juanma010901/Quadruped-Robot/Diseños/files/F_cover.stl

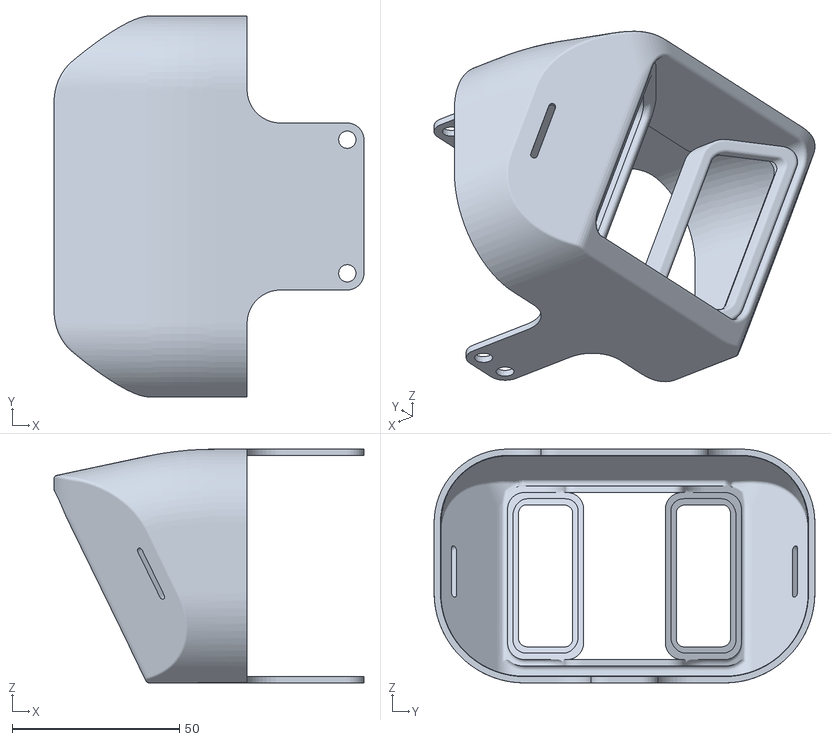
[picture p19: CAD file, 2023-06-25]
Diseños/files/F_cover.stl
92.8 x 114.0 x 70.0
