juanma010901/Quadruped-Robot/Diseños/files/V1.00_Nose.stl

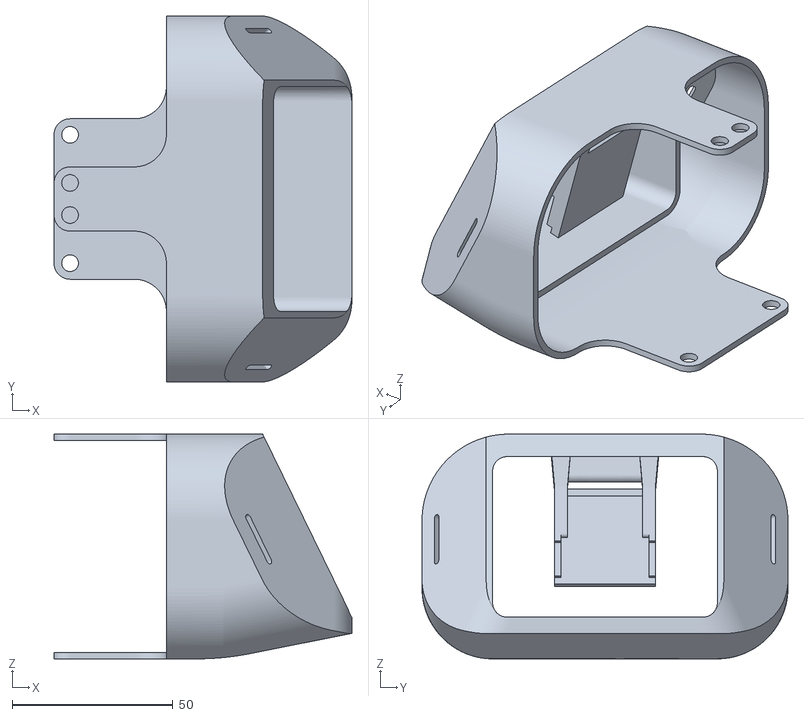
[picture p20: CAD file, 2023-06-25]
Diseños/files/V1.00_Nose.stl
92.8 x 114.0 x 70.0
