juanma010901/Quadruped-Robot/Diseños/files/Rear_Cover.stl

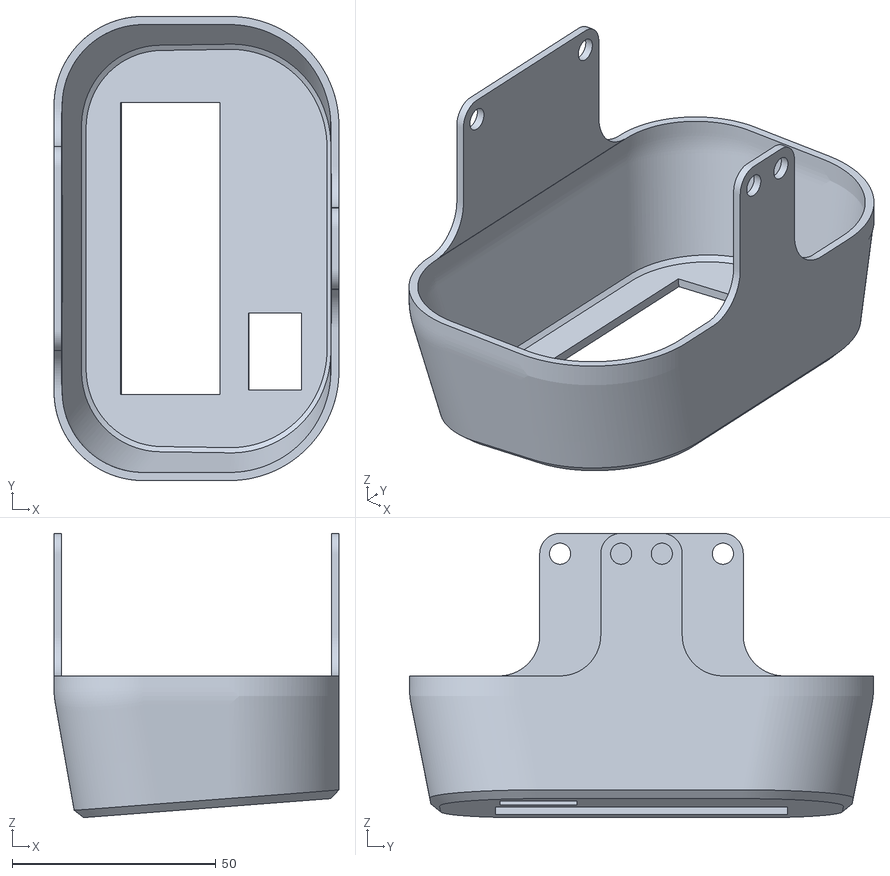
[picture p21: CAD file, 2023-06-25]
Diseños/files/Rear_Cover.stl
70.0 x 114.0 x 69.8
