juanma010901/Quadruped-Robot/Diseños/files/V1.01_Front_Shoulder_Inner.stl

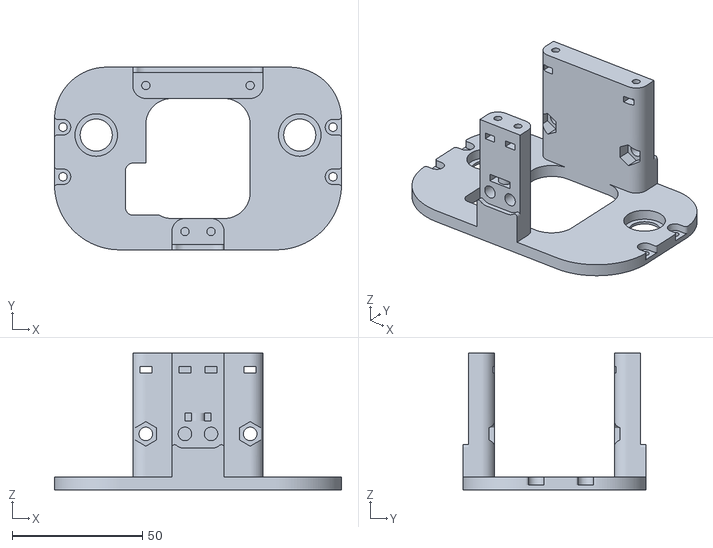
[picture p22: CAD file, 2023-06-25]
Diseños/files/V1.01_Front_Shoulder_Inner.stl
110.0 x 70.0 x 52.5
