juanma010901/Quadruped-Robot/Diseños/files/V1.00_Foot.stl

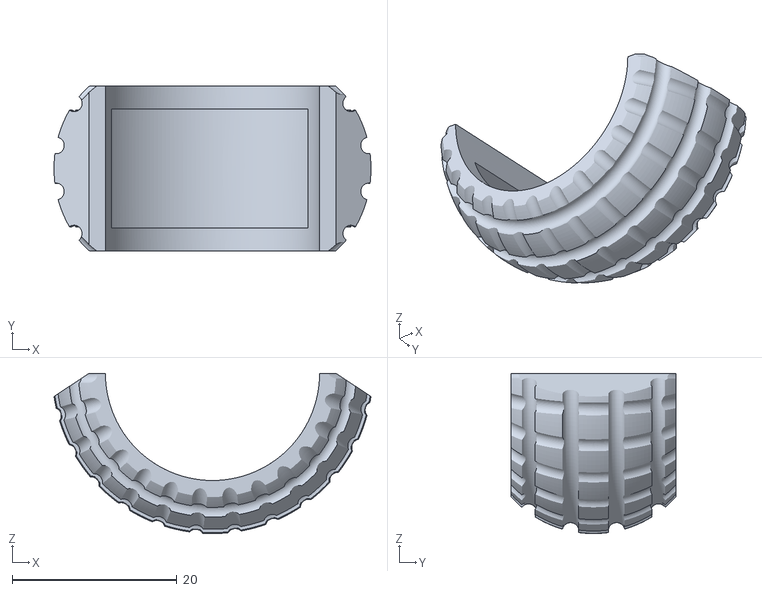
[picture p23: CAD file, 2023-06-25]
Diseños/files/V1.00_Foot.stl
38.5 x 20.0 x 19.4
