juanma010901/Quadruped-Robot/Diseños/files/Outer_Shoulder.stl

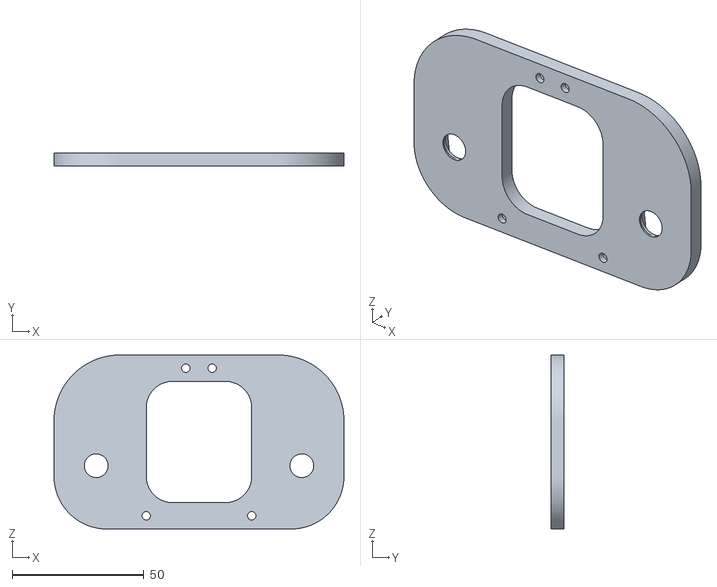
[picture p24: CAD file, 2023-06-25]
Diseños/files/Outer_Shoulder.stl
110.0 x 5.00 x 66.0
